niklasekstrom/a314/Software/a314device/sockets.c

#include <proto/exec.h>

#include "sockets.h"
#include "debug.h"

#define SysBase (*(struct ExecBase **)4)

extern void NewList(struct List *l);

void init_sockets(struct A314Device *dev)
{
	NewList(&dev->active_sockets);
	dev->send_queue_head = NULL;
	dev->send_queue_tail = NULL;
	dev->next_stream_id = 1;
}

struct Socket *find_socket(struct A314Device *dev, void *sig_task, ULONG socket)
{
	dbg_trace("Enter: find_socket, socket=$l", socket);

	for (struct Node *node = dev->active_sockets.lh_Head; node->ln_Succ != NULL; node = node->ln_Succ)
	{
		struct Socket *s = (struct Socket *)node;
		if (s->sig_task == sig_task && s->socket == socket)
			return s;
	}
	return NULL;
}

struct Socket *find_socket_by_stream_id(struct A314Device *dev, UBYTE stream_id)
{
	dbg_trace("Enter: find_socket_by_stream_id, stream_id=$b", stream_id);

	for (struct Node *node = dev->active_sockets.lh_Head; node->ln_Succ != NULL; node = node->ln_Succ)
	{
		struct Socket *s = (struct Socket *)node;
		if (s->stream_id == stream_id)
			return s;
	}
	return NULL;
}

static UBYTE allocate_stream_id(struct A314Device *dev)
{
	dbg_trace("Enter: allocate_stream_id");

	for (int i = 0; i < 256; i++)
	{
		UBYTE stream_id = dev->next_stream_id;
		dev->next_stream_id += 2;
		if (find_socket_by_stream_id(dev, stream_id) == NULL)
		{
			dbg_trace("Leave: allocate_stream_id, stream_id=$b", stream_id);
			return stream_id;
		}
	}

	// BUG: What to do here? This is quite bad.
	// Need to propagate this error condition to the calling application.
	dbg_error("There were no free stream ids, and there is no code to handle this case");
	return dev->next_stream_id;
}

static void free_stream_id(struct A314Device *dev, UBYTE stream_id)
{
	dbg_trace("Enter: free_stream_id, stream_id=$b", stream_id);
	// Currently do nothing.
	// Could speed up allocate_stream_id using a bitmap?
}

struct Socket *create_socket(struct A314Device *dev, struct Task *task, ULONG id)
{
	dbg_trace("Enter: create_socket, socket_id=$l", id);

	struct Socket *s = (struct Socket *)AllocMem(sizeof(struct Socket), MEMF_CLEAR);
	s->sig_task = task;
	s->socket = id;
	s->stream_id = allocate_stream_id(dev);
	AddTail(&dev->active_sockets, (struct Node *)s);
	return s;
}

void delete_socket(struct A314Device *dev, struct Socket *s)
{
	dbg_trace("Enter: delete_socket, socket_id=$l", s->socket);

	Remove((struct Node *)s);
	free_stream_id(dev, s->stream_id);
	FreeMem(s, sizeof(struct Socket));
}

void add_to_send_queue(struct A314Device *dev, struct Socket *s, UWORD required_length)
{
	dbg_trace("Enter: add_to_send_queue, socket_id=$l, required_length=$w", s->socket, required_length);

	s->send_queue_required_length = required_length;
	s->next_in_send_queue = NULL;

	if (dev->send_queue_head == NULL)
		dev->send_queue_head = s;
	else
		dev->send_queue_tail->next_in_send_queue = s;
	dev->send_queue_tail = s;

	s->flags |= SOCKET_IN_SEND_QUEUE;
}

void remove_from_send_queue(struct A314Device *dev, struct Socket *s)
{
	dbg_trace("Enter: remove_from_send_queue, socket_id=$l", s->socket);

	if (s->flags & SOCKET_IN_SEND_QUEUE)
	{
		if (dev->send_queue_head == s)
		{
			dev->send_queue_head = s->next_in_send_queue;
			if (dev->send_queue_head == NULL)
				dev->send_queue_tail = NULL;
		}
		else
		{
			struct Socket *curr = dev->send_queue_head;
			while (curr->next_in_send_queue != s)
				curr = curr->next_in_send_queue;

			curr->next_in_send_queue = s->next_in_send_queue;
			if (dev->send_queue_tail == s)
				dev->send_queue_tail = curr;
		}

		s->next_in_send_queue = NULL;
		s->flags &= ~SOCKET_IN_SEND_QUEUE;
	}
}
